aiirononeko/wakizashi/firmware/build.rs

use const_gen::*;
use std::fs::File;
use std::io::{Read, Write};
use std::path::{Path, PathBuf};
use std::{env, fs};
use xz2::read::XzEncoder;

fn main() {
    println!("cargo:rerun-if-changed=vial.json");
    println!("cargo:rerun-if-changed=keyboard.toml");

    generate_vial_config();

    let out = &PathBuf::from(env::var_os("OUT_DIR").unwrap());
    File::create(out.join("memory.x"))
        .unwrap()
        .write_all(include_bytes!("memory.x"))
        .unwrap();
    println!("cargo:rustc-link-search={}", out.display());

    println!("cargo:rerun-if-changed=memory.x");

    println!("cargo:rustc-link-arg=--nmagic");
    println!("cargo:rustc-link-arg=-Tlink.x");
    println!("cargo:rustc-link-arg=-Tdefmt.x");

    println!("cargo:rustc-linker=flip-link");
}

fn generate_vial_config() {
    let out_file = Path::new(&env::var_os("OUT_DIR").unwrap()).join("config_generated.rs");

    let p = Path::new("vial.json");
    let mut content = String::new();
    File::open(p)
        .unwrap_or_else(|e| panic!("Cannot find vial.json {:?}: {}", p, e))
        .read_to_string(&mut content)
        .expect("Cannot read vial.json");

    let vial_cfg = json::stringify(json::parse(&content).unwrap());
    let mut keyboard_def_compressed: Vec<u8> = Vec::new();
    XzEncoder::new(vial_cfg.as_bytes(), 6)
        .read_to_end(&mut keyboard_def_compressed)
        .unwrap();

    let keyboard_id: Vec<u8> = vec![0xAA, 0xBB, 0xCC, 0xDD, 0x57, 0x4B, 0x00, 0x02];
    let const_declarations = [
        const_declaration!(pub VIAL_KEYBOARD_DEF = keyboard_def_compressed),
        const_declaration!(pub VIAL_KEYBOARD_ID = keyboard_id),
    ]
    .map(|s| "#[allow(clippy::redundant_static_lifetimes)]\n".to_owned() + s.as_str())
    .join("\n");
    fs::write(out_file, const_declarations).unwrap();
}
